Projects-and-Stuff/Temp-Control-SSR/Hardware/TempControl.sch

## KiCad design Hardware/TempControl.sch (2011-11-30)

Schematic: TempControl.sch

Parts:
C1, C3, C5: 22nF
C2, C4: 3.3uF
C6, C7: 12pF
C8: .022uF
D1: BRIDGE
D2: LED_Power
D3: LED_Status
F1: 250V 8A
F2: 250VAC 315mA
IC1: ATTINY84-SS; SO14
K1: S202S01; relay-S102T0X
P1: Input
P2: Output
R1, R2, R3, R4: 4.7k
R5, R6: 300
R7: 158
R8: 47
R9: VARISTORS05K230; varistor-S05K230
SW1: SPST
T1: BV030-7585.0
U1: MCP1802T
U2: DS18B20
X1: ISP
X2: 20.0 MHz
